NeuroTinker/NeuroBytes_Force_Sensor/HARDWARE/copper.png

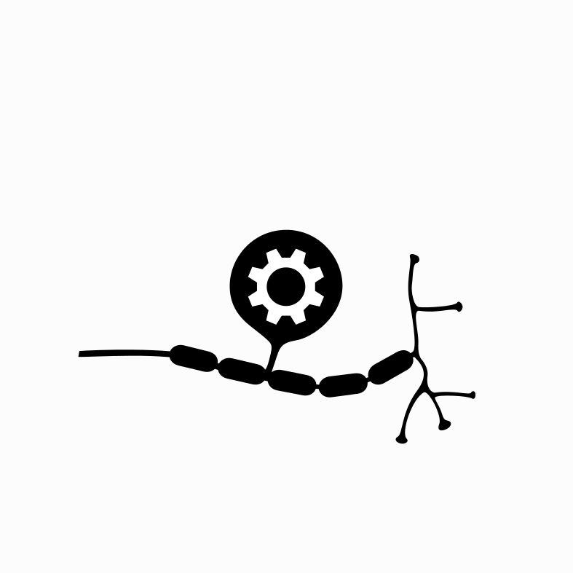
HARDWARE/copper.png
